thias15/OpenBot-1/docs/images/app_teaser.jpg

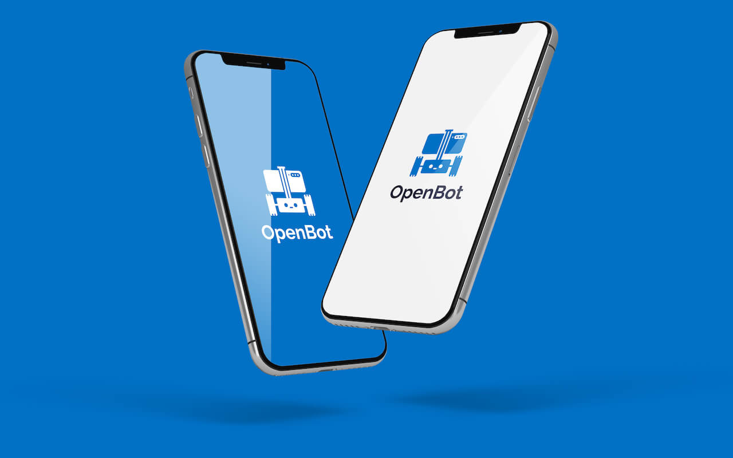
docs/images/app_teaser.jpg
