thias15/OpenBot-1/docs/images/pcb_2d_v1.png

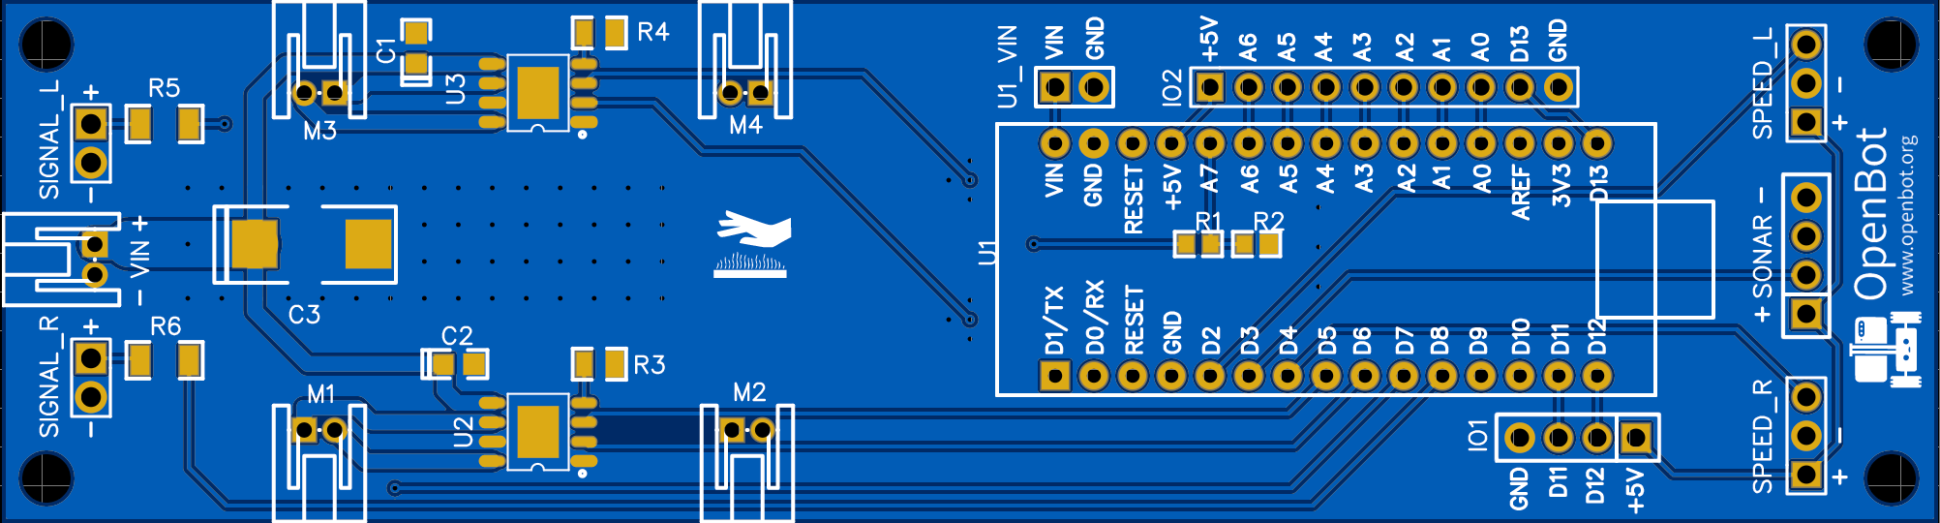
docs/images/pcb_2d_v1.png
