thias15/OpenBot-1/traffic/plots.png

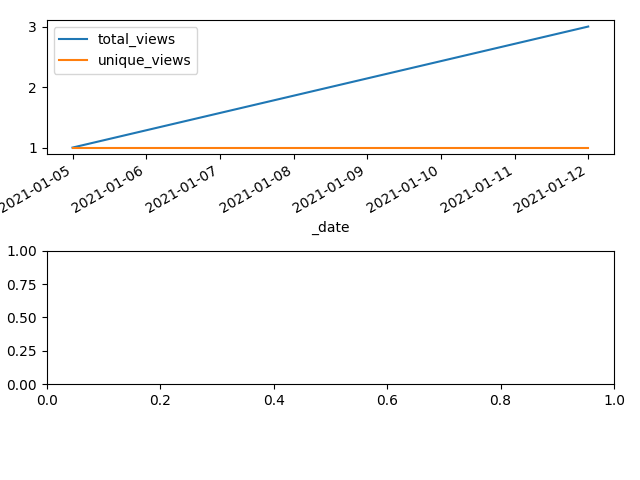
traffic/plots.png
